sebseb7/lun1k/firmware/drivers/config.c

#include "eeprom.h"

uint16_t VarDataTab[NB_OF_VAR] = {0, 0, 0};

void dummy(void)
{
  FLASH_Unlock();
  EE_Init();
  EE_ReadVariable(0, &VarDataTab[0]);
  EE_ReadVariable(1, &VarDataTab[1]);
  EE_ReadVariable(2, &VarDataTab[2]);
  FLASH_Lock();

}
